omarsbu/500A-Multicell-Battery-Load-Analyzer/Software/adc.c

#include "main.h"

ISR(ADC0_RESRDY_vect)
{
	// Empty ISR — needed to wake from ADC sleep mode
}

//***************************************************************************
//
// Function Name : "ADC_init"
// Target MCU : AVR128DB48
// DESCRIPTION
// Initializes the ADC0 module of the AVR128DB48 for differential or
// single-ended mode, VDD reference, 12-bit resolution, free-run mode,
// 16 sample accumulation, and clock prescalar divided by 4.
// Enables interrupts and ADC0 module.
//
// Inputs : 
//		uint8_t mode: 0 -> single ended, 1 -> differential
//
// Outputs : None
//
//**************************************************************************
void ADC_init(uint8_t mode)
{
	adc_mode = mode;	// single-ended or differential mode
	
	// Use 2.048V as reference
	VREF.ADC0REF = VREF_REFSEL_2V048_gc;
	
	// 12-bit resolution, Free-Run mode, differential/single-ended, Right adjusted, Enable
	ADC0.CTRLA = (ADC_RESSEL_12BIT_gc | (ADC_FREERUN_bm) | (adc_mode << 5) | ADC_ENABLE_bm);

	//enables interrupt
	ADC0.INTCTRL |= ADC_RESRDY_bm;

	// Set to accumulate 64 samples
	ADC0.CTRLB = ADC_SAMPNUM_ACC64_gc;
	
	// Divided CLK_PER by 16
	ADC0.CTRLC = ADC_PRESC_DIV16_gc;
}

//***************************************************************************
//
// Function Name : "ADC_startConversion"
// Target MCU : AVR128DB48
// DESCRIPTION
// Starts a conversion on ADC0.
//
// Inputs : None
//
// Outputs : None
//
//
//**************************************************************************
void ADC_startConversion(void)
{
	ADC0.COMMAND = ADC_STCONV_bm;// starts ADC conversion
}

//***************************************************************************
//
// Function Name : "ADC_stopConversion"
// Target MCU : AVR128DB48
// DESCRIPTION
// Stops a conversion on ADC0.
//
// Inputs : None
//
// Outputs : None
//
//
//**************************************************************************
void ADC_stopConversion(void)
{
	ADC0.COMMAND = ADC_SPCONV_bm;	// stops ADC conversion
}

//***************************************************************************
//
// Function Name : "ADC_isConversionDone"
// Target MCU : AVR128DB48
// Target Hardware : None
// DESCRIPTION
// Reads the INTFLAGS register of ADC0 to determine if the
// ADC conversion is finished
//
// Inputs : None
//
// Outputs : uint8_t result: if result is all 0s, conversion is not finished,
// if result is 0x01, conversion has finished
//
//
//**************************************************************************
uint8_t ADC_isConversionDone(void)
{
	return (ADC0.INTFLAGS & ADC_RESRDY_bm);	//checks if RESRDY bit is set
}
//***************************************************************************
//
// Function Name : "ADC_channelSEL"
// Target MCU : AVR128DB48
// DESCRIPTION
// Selects 1 (single ended mode) or 2 channels (differential mode)
//	for ADC0 to read the voltage from
//
// Inputs : 
//		uint8_t AIN_POS: Positive differential or single-ended input
//		uint8_t AIN_NEG: Negative differential input
//
// Outputs : None
//
//
//**************************************************************************
void ADC_channelSEL(uint8_t AIN_POS, uint8_t AIN_NEG)
{
	/* In differential mode, write both MUXPOS and MUXNEG registers */
	if (adc_mode == 0x01)
	{
		ADC0.MUXPOS = AIN_POS;
		ADC0.MUXNEG = AIN_NEG;
	}
	/* In single-ended mode, only write MUXPOS register */
	else
		ADC0.MUXPOS = AIN_POS;
}
//***************************************************************************
//
// Function Name : "ADC_read"
// Target MCU : AVR128DB48
// DESCRIPTION
//	Reads an integer value from the ADC and converts it to a floating point
//	voltage based on reference voltage and conversion resolution
//
// Inputs : None
//
// Outputs : 
//		float result: A floating point voltage converted by the ADC
//
//**************************************************************************
float ADC_read(void)
{	
	/* ADC conversions in free running mode */
	ADC_startConversion();
	
	while(ADC_isConversionDone() != 0x01);	// wait for conversion to finish
	ADC_stopConversion();
	
	/* 12 bit result was left adjusted, so shift right 4 places to fix, reading ADC.RES clears interrupt flag */
	if (adc_mode == 0x00)		
		return (float)(adc_vref * (ADC0.RES >> 4) / 4096);	// single-ended resolution is 12 bits -> 4096 values
	else
		return (float)(adc_vref * (ADC0.RES >> 4) / 2048);	// differential resolution is 11 bits -> 2048 values
}
//***************************************************************************
//
// Function Name : "batteryCell_read"
// Target MCU : AVR128DB48
// DESCRIPTION
// Starts a conversion on ADC0 for one battery in the quad pack,
// reads the result, and converts the result back to an
// analog voltage
//
// Inputs : 
//	uint8_t BAT_POS: Positive battery terminal
//	uint8_t BAT_NEG: Negative battery terminal
//
// Outputs :
//	float result: the analog voltage across the battery
//
//**************************************************************************
float batteryCell_read(uint8_t BAT_POS, uint8_t BAT_NEG)
{	
	/* Differential measurement */
	ADC_init(0x01);	
	
	if (voltage_precision == 0x01) //Low precision = 3.3 V voltage reference			
	{				
		VREF.ADC0REF = VREF_REFSEL_VDD_gc;
		adc_vref = 3.3;
	}
	else //high precision = 2.048 V voltage reference
	{
		VREF.ADC0REF = VREF_REFSEL_2V048_gc;
		adc_vref = 2.048;
	}
	/* Select ADC channel and wait for it to settle*/	
	ADC_channelSEL(BAT_POS, BAT_NEG);
	_delay_ms(10);
	adc_value = ADC_read();
	
	/* Multiply by voltage divider ratio to undo attenuation */
	return (float) (adc_value * battery_voltage_divider_ratios);
}
//***************************************************************************
//
// Function Name : "read_UNLOADED_battery_voltages"
// Target MCU : AVR128DB48
// DESCRIPTION
//  Reads the voltage across each battery cell input and stores the results 
//	in the UNLOADED_battery_voltgaes array
// Inputs : none
//
// Outputs : none
//
//
//**************************************************************************
void read_UNLOADED_battery_voltages(void)
{
	/* Read voltage of each cell and store in array when unloaded */
	current_test_result.UNLOADED_battery_voltages[0] = batteryCell_read(B1_ADC_CHANNEL, GND_ADC_CHANNEL);	// B1_POS - GND
	current_test_result.UNLOADED_battery_voltages[1] = batteryCell_read(B2_ADC_CHANNEL, B1_ADC_CHANNEL);	// B2_POS - B1_POS
	current_test_result.UNLOADED_battery_voltages[2] = batteryCell_read(B3_ADC_CHANNEL, B2_ADC_CHANNEL);	// B3_POS - B2_POS
	current_test_result.UNLOADED_battery_voltages[3] = batteryCell_read(B4_ADC_CHANNEL, B3_ADC_CHANNEL);	// B4_POS - B3_POS
}
//***************************************************************************
//
// Function Name : "read_LOADED_battery_voltages"
// Target MCU : AVR128DB48
// DESCRIPTION
//  Reads the voltage across each battery cell input and stores the results
//	in the LOADED_battery_voltgaes array
// Inputs : none
//
// Outputs : none
//
//
//**************************************************************************
void read_LOADED_battery_voltages(void)
{
	/* Read voltage of each cell and store in array once load current reaches 500A */
	current_test_result.LOADED_battery_voltages[0] = batteryCell_read(B1_ADC_CHANNEL, GND_ADC_CHANNEL);	// B1_POS - GND
	current_test_result.LOADED_battery_voltages[1] = batteryCell_read(B2_ADC_CHANNEL, B1_ADC_CHANNEL);	// B2_POS - B1_POS
	current_test_result.LOADED_battery_voltages[2] = batteryCell_read(B3_ADC_CHANNEL, B2_ADC_CHANNEL);	// B3_POS - B2_POS
	current_test_result.LOADED_battery_voltages[3] = batteryCell_read(B4_ADC_CHANNEL, B3_ADC_CHANNEL);	// B4_POS - B3_POS
}

//***************************************************************************
//
// Function Name : "OPAMP_Instrumentation_init"
// Target MCU : AVR128DB48
// DESCRIPTION
// This function reads output of the instrumentation amplifier and converts
//	it to a current based on the shunt resistance value.
//
// Inputs : none
//
// Outputs : none
//		float load_current: Analog Load current through shunt in amps
//
//**************************************************************************
float load_current_Read(void)
{	
	/* Put ADC in single-ended mode */
	ADC_init(0x00);
	adc_vref = 2.048; //use 2.048 voltage reference
	
	ADC_channelSEL(OPAMP_ADC_CHANNEL, GND_ADC_CHANNEL); //select OPAMP ADC Channel and GND ADC Channel
	adc_value = ADC_read();		
	
	/* Multiply by divider ratio to undo attenuation, divide by gain to undo gain, divide by resistance to convert to amps */
	load_current_amps = ((adc_value - 0.096) / (OPAMP_gain*shunt_resistance_ohms));	

	if (voltage_precision == 0x01) //Low precision = 3.3 V voltage reference			
	{				
		VREF.ADC0REF = VREF_REFSEL_VDD_gc;
		adc_vref = 3.3;
	}
	
	
	if(load_current_amps < 0.2) //if load current is less than 0.2, return 0
		return 0;
	else //else return load_current_amps
		return load_current_amps;
}
